shm-dmitry/auto_close_window/3d/mechanics-v2-window-clampwindow-clamp-4.stl

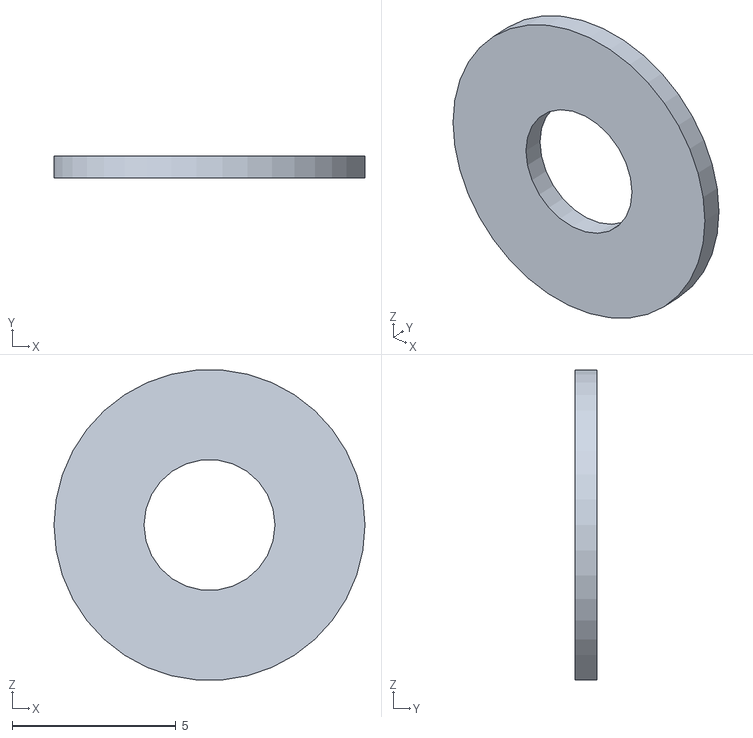
[picture p15: CAD file, 2024-10-09]
3d/mechanics-v2-window-clampwindow-clamp-4.stl
9.50 x 0.68 x 9.47
