shm-dmitry/auto_close_window/3d/mechanics-v2-pdu2pdu-box-up.stl

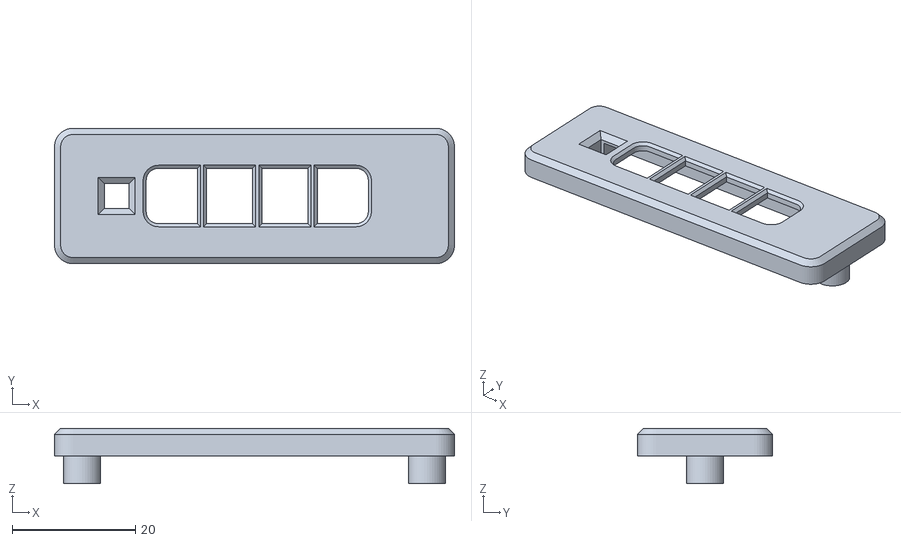
[picture p16: CAD file, 2024-10-09]
3d/mechanics-v2-pdu2pdu-box-up.stl
65.0 x 22.0 x 9.00
