shm-dmitry/auto_close_window/3d/mechanics-v2-mmmm-charge-button.stl

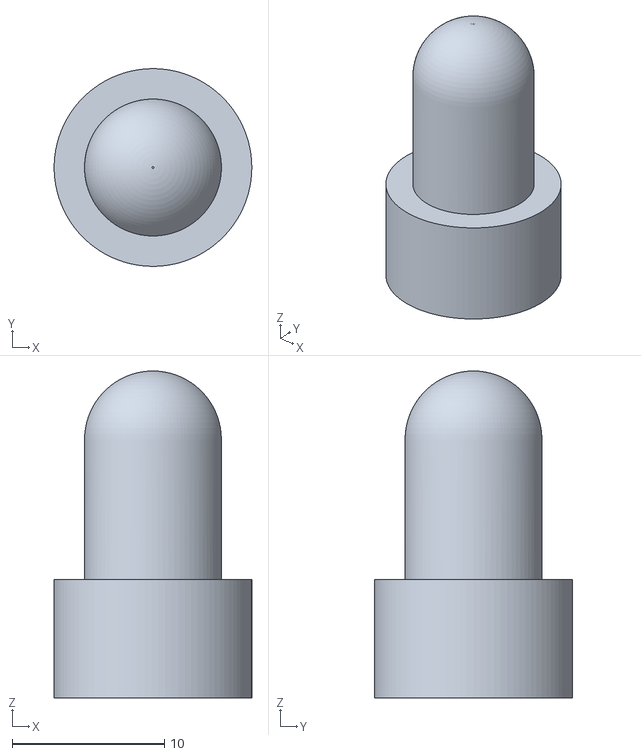
[picture p17: CAD file, 2024-10-09]
3d/mechanics-v2-mmmm-charge-button.stl
13.0 x 13.0 x 21.5
