shm-dmitry/auto_close_window/3d/mechanics-v2-servo_platesw420-adapter.stl

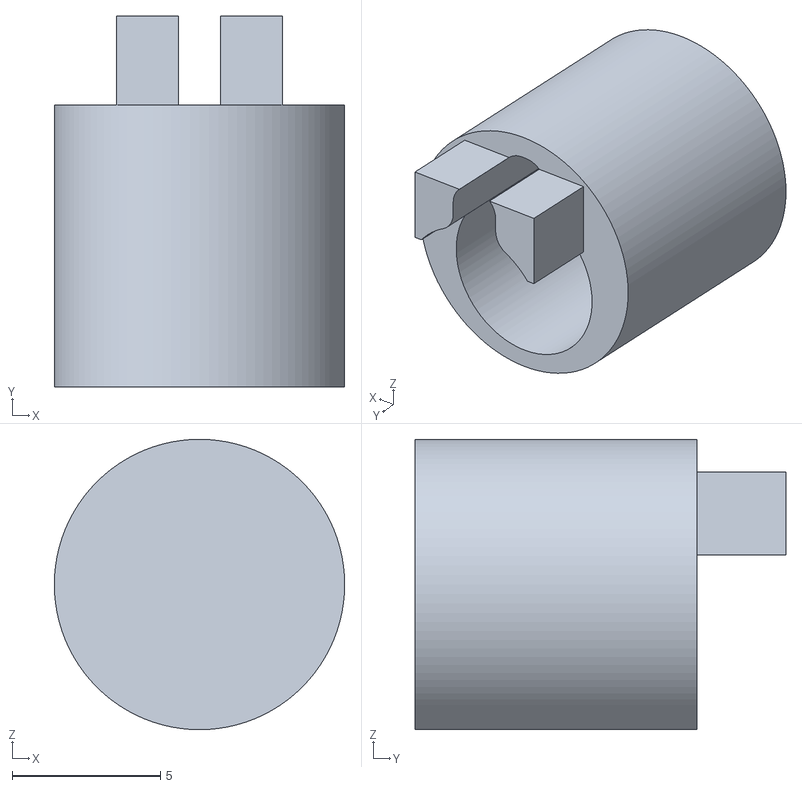
[picture p18: CAD file, 2024-10-09]
3d/mechanics-v2-servo_platesw420-adapter.stl
9.80 x 12.5 x 9.80
