shm-dmitry/auto_close_window/3d/mechanics-v2-hmhm-down.stl

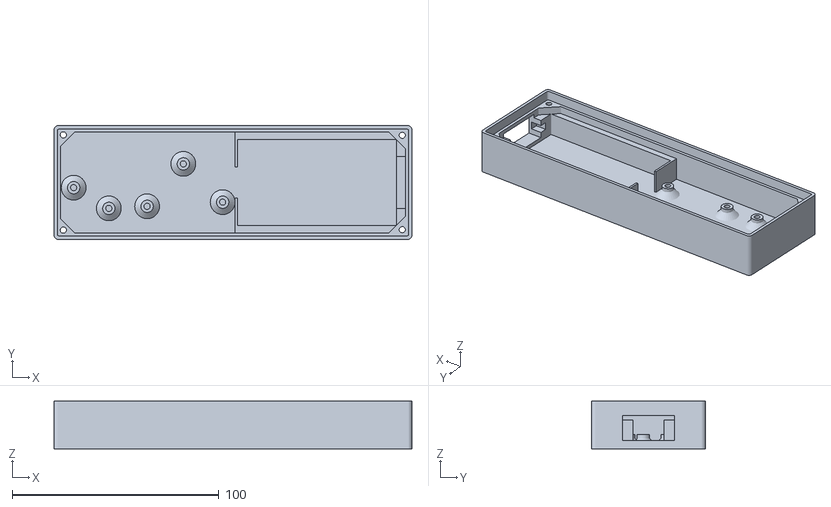
[picture p19: CAD file, 2024-10-09]
3d/mechanics-v2-hmhm-down.stl
173.0 x 55.0 x 23.0
