shm-dmitry/auto_close_window/3d/mechanics-v2-servo_platedebug-wall-support.stl

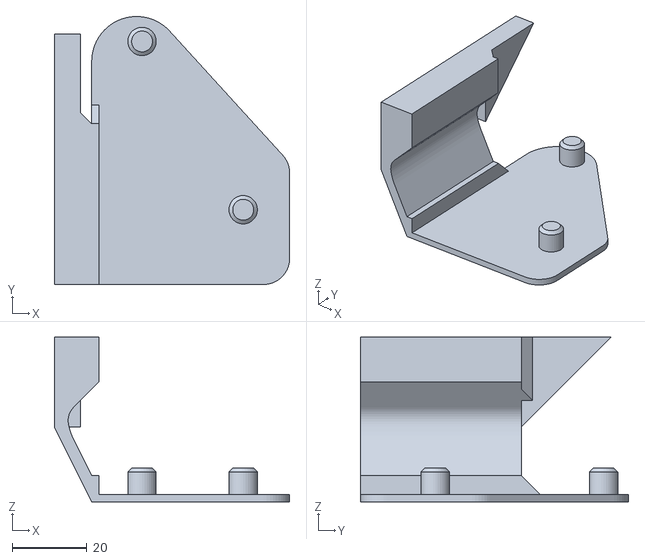
[picture p20: CAD file, 2024-10-09]
3d/mechanics-v2-servo_platedebug-wall-support.stl
63.0 x 71.7 x 44.0
