shm-dmitry/auto_close_window/3d/mechanics-v2-mmmm-charger-port.stl

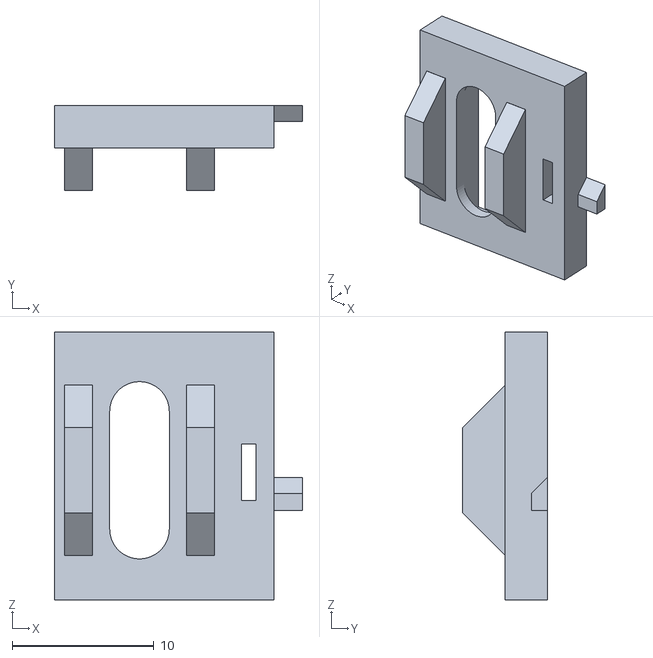
[picture p21: CAD file, 2024-10-09]
3d/mechanics-v2-mmmm-charger-port.stl
17.5 x 6.00 x 18.9
