shm-dmitry/auto_close_window/3d/mechanics-v2-mmmm-charger-cup.stl

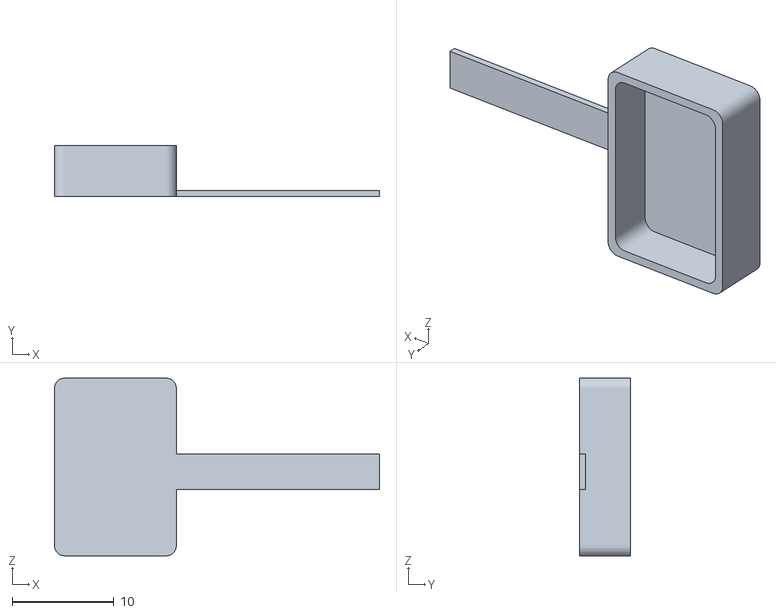
[picture p22: CAD file, 2024-10-09]
3d/mechanics-v2-mmmm-charger-cup.stl
32.0 x 5.00 x 17.5
