shm-dmitry/auto_close_window/3d/mechanics-v2-hmhm-glass.stl

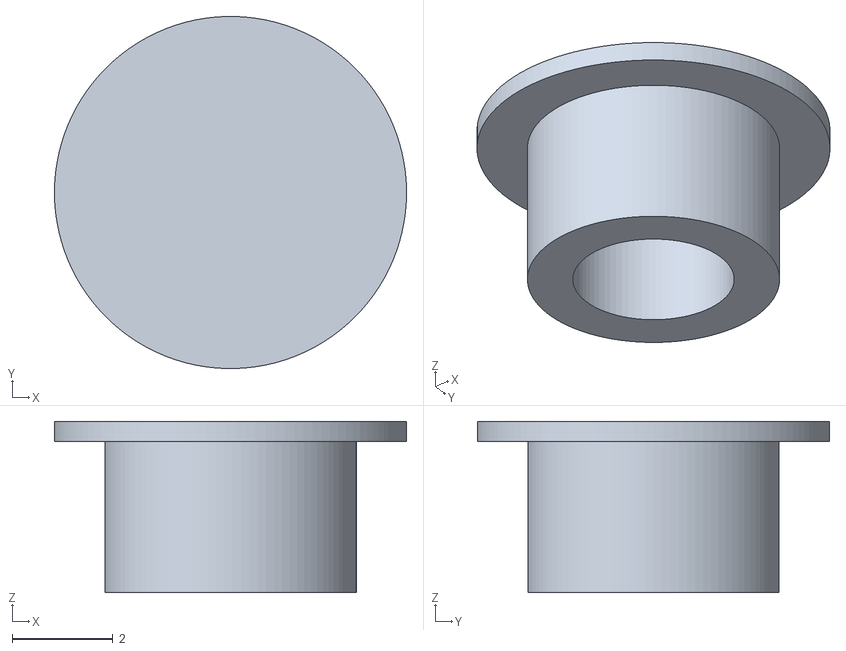
[picture p23: CAD file, 2024-10-09]
3d/mechanics-v2-hmhm-glass.stl
7.00 x 7.00 x 3.40
