shm-dmitry/auto_close_window/3d/mechanics-v2-servolimiters.stl

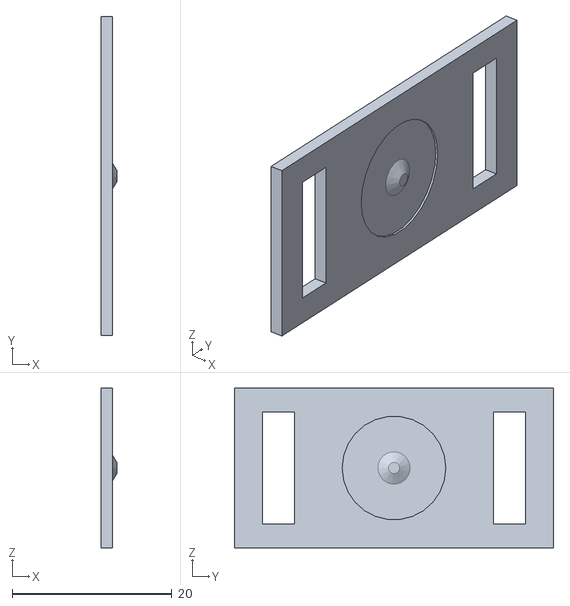
[picture p24: CAD file, 2024-10-09]
3d/mechanics-v2-servolimiters.stl
2.00 x 40.0 x 20.0
