shm-dmitry/auto_close_window/3d/mechanics-v2-servoservo-hand.stl

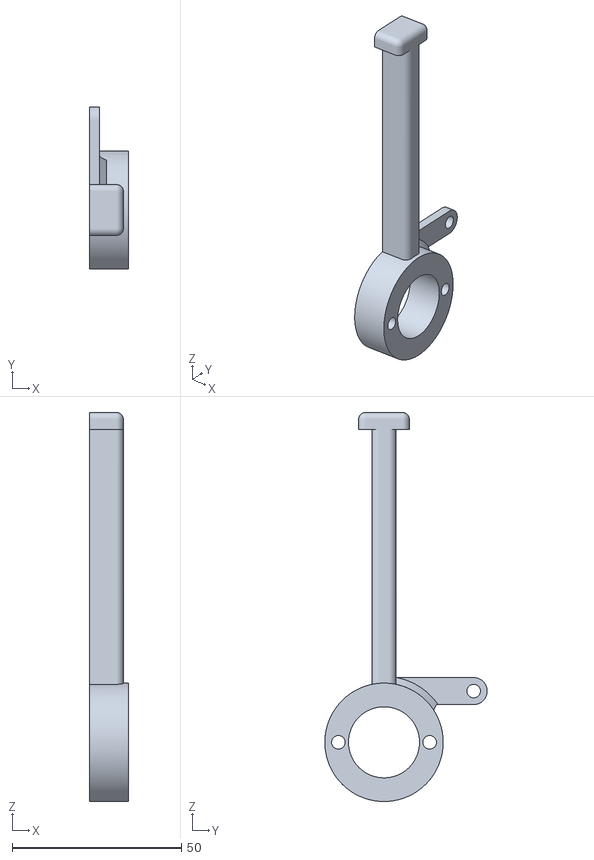
[picture p25: CAD file, 2024-10-09]
3d/mechanics-v2-servoservo-hand.stl
11.5 x 48.0 x 115.0
