shm-dmitry/auto_close_window/3d/mechanics-v2-servo_plateservo-holder-cabel.stl

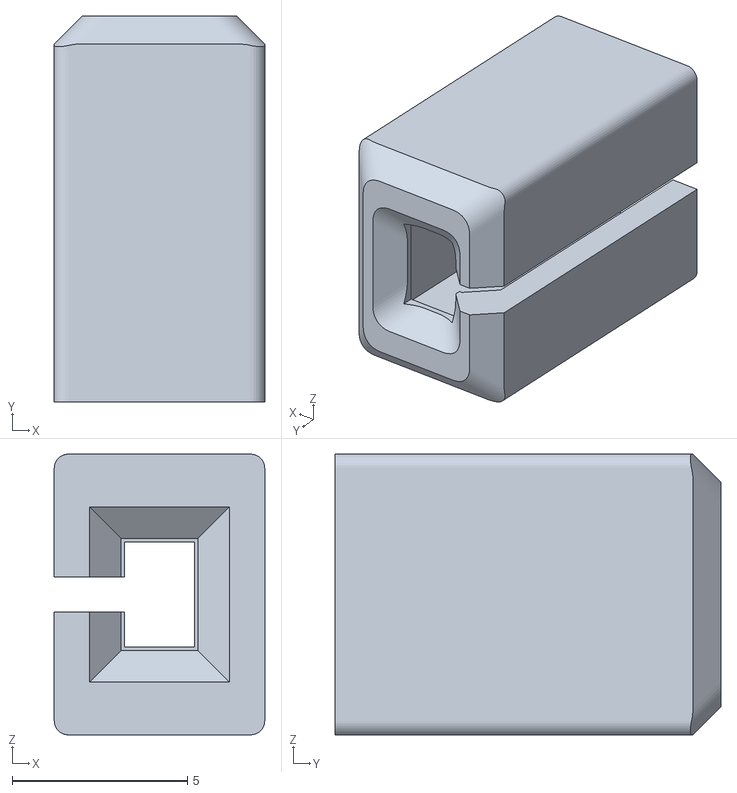
[picture p26: CAD file, 2024-10-09]
3d/mechanics-v2-servo_plateservo-holder-cabel.stl
6.00 x 11.0 x 8.00
