shm-dmitry/auto_close_window/3d/mechanics-v2-servolimit-switch-extboard-holder.stl

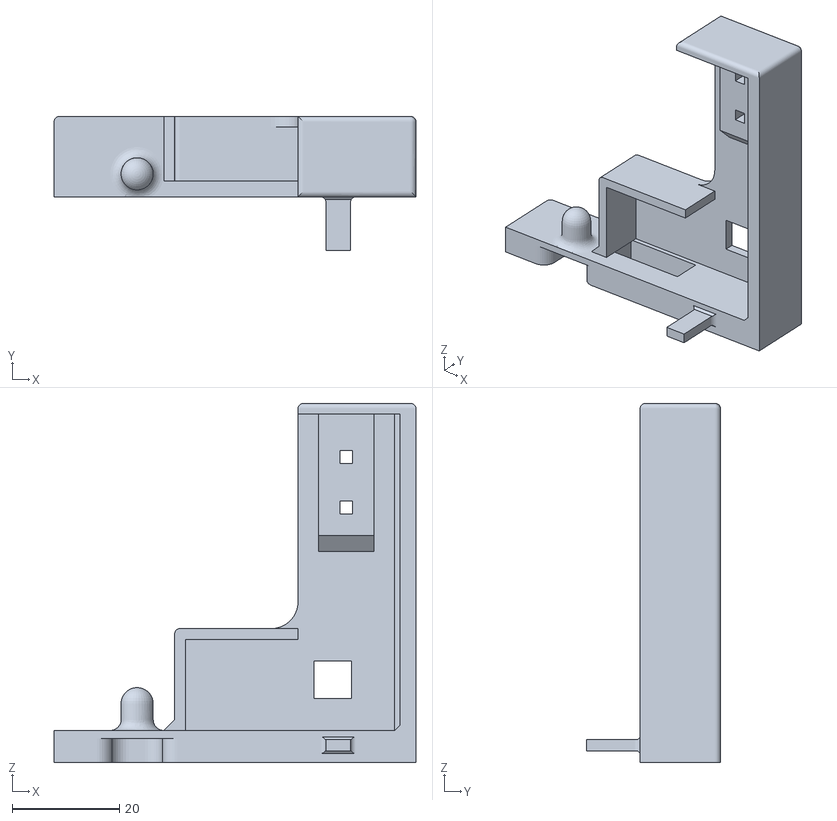
[picture p27: CAD file, 2024-10-09]
3d/mechanics-v2-servolimit-switch-extboard-holder.stl
67.5 x 25.0 x 67.0
