shm-dmitry/auto_close_window/3d/mechanics-v2-servolimit-switch-cabel-holder.stl

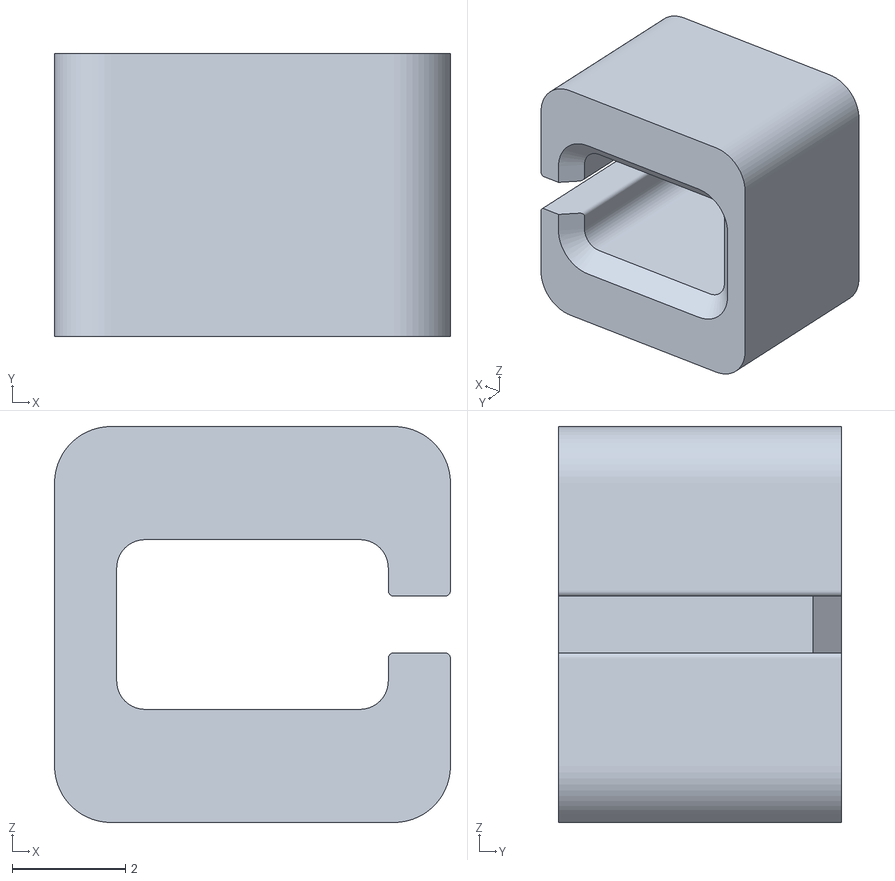
[picture p28: CAD file, 2024-10-09]
3d/mechanics-v2-servolimit-switch-cabel-holder.stl
7.00 x 5.00 x 7.00
