shm-dmitry/auto_close_window/3d/mechanics-v2-servo_platemicrophone-air-ring.stl

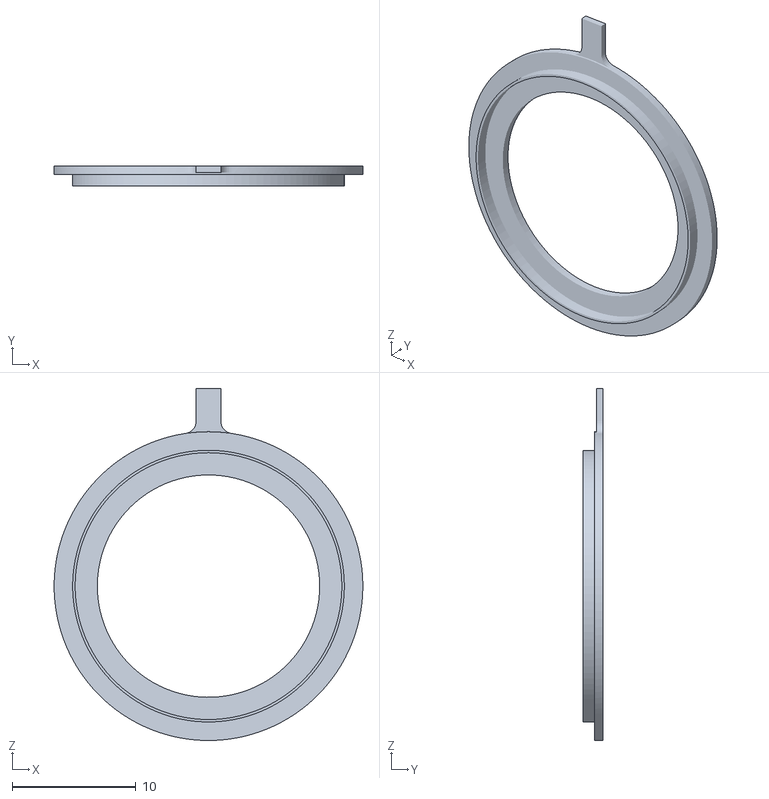
[picture p29: CAD file, 2024-10-09]
3d/mechanics-v2-servo_platemicrophone-air-ring.stl
25.0 x 1.64 x 28.5
