shm-dmitry/auto_close_window/3d/mechanics-v2-hmhm-button.stl

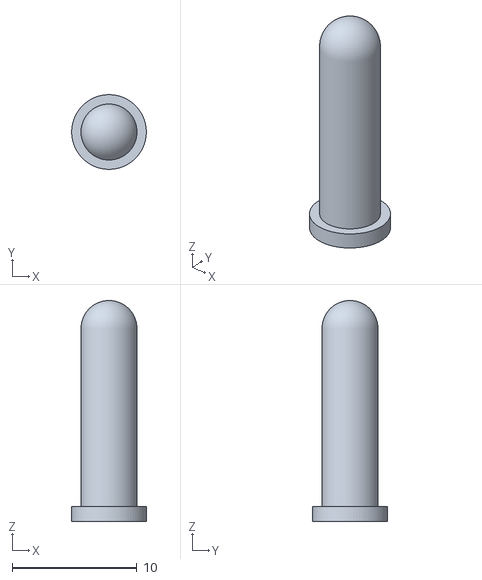
[picture p30: CAD file, 2024-10-09]
3d/mechanics-v2-hmhm-button.stl
6.00 x 6.00 x 17.8
