shm-dmitry/auto_close_window/3d/mechanics-v2-window-clamplimit-switch-cup-small.stl

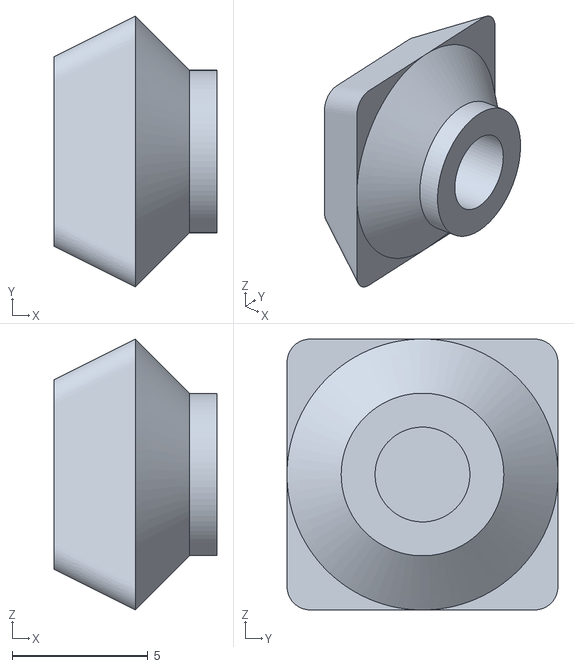
[picture p31: CAD file, 2024-10-09]
3d/mechanics-v2-window-clamplimit-switch-cup-small.stl
6.00 x 10.0 x 10.0
