shm-dmitry/auto_close_window/3d/mechanics-v2-window-clampwindow-clamp-1.stl

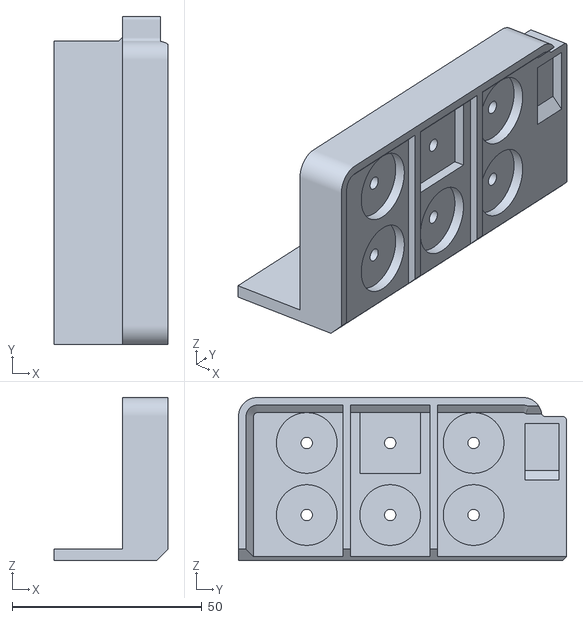
[picture p32: CAD file, 2024-10-09]
3d/mechanics-v2-window-clampwindow-clamp-1.stl
30.0 x 86.5 x 43.0
