shm-dmitry/auto_close_window/3d/mechanics-v2-rubberrubber-tensioner.stl

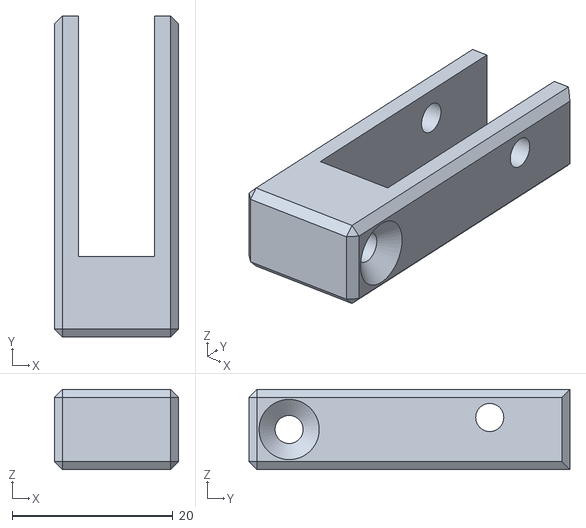
[picture p33: CAD file, 2024-10-09]
3d/mechanics-v2-rubberrubber-tensioner.stl
15.5 x 40.0 x 10.0
