shm-dmitry/auto_close_window/3d/mechanics-v2-window-clamplimit-switch-cup.stl

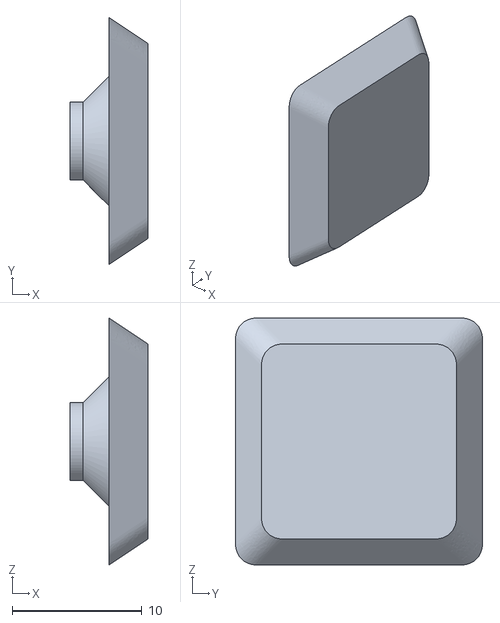
[picture p34: CAD file, 2024-10-09]
3d/mechanics-v2-window-clamplimit-switch-cup.stl
6.00 x 19.0 x 19.0
