shm-dmitry/auto_close_window/3d/mechanics-v2-hmhm-charger-port-cup.stl

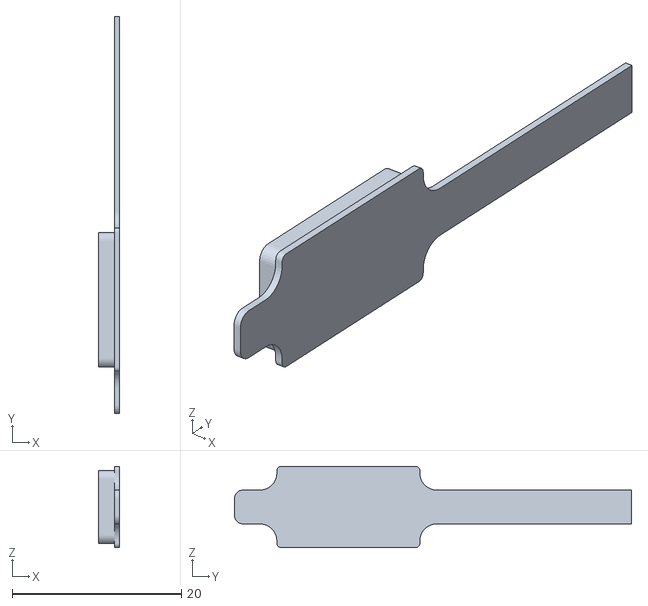
[picture p35: CAD file, 2024-10-09]
3d/mechanics-v2-hmhm-charger-port-cup.stl
2.50 x 46.9 x 9.60
