shm-dmitry/auto_close_window/3d/mechanics-v2-window-clampwindow-clamp-2.stl

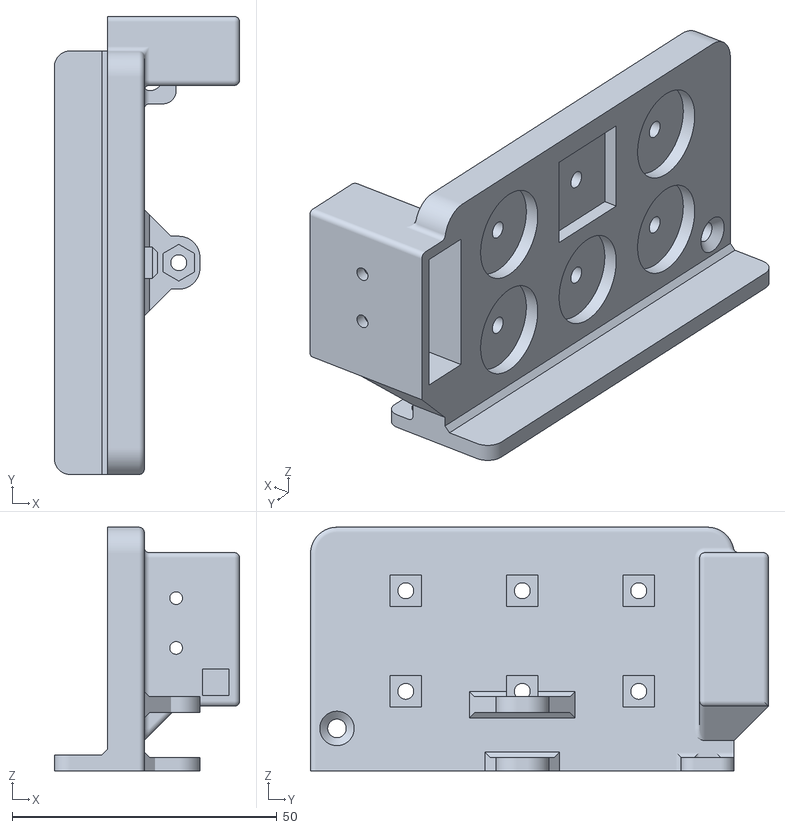
[picture p36: CAD file, 2024-10-09]
3d/mechanics-v2-window-clampwindow-clamp-2.stl
35.0 x 86.5 x 46.0
