shm-dmitry/auto_close_window/3d/mechanics-v2-hmhm-up.stl

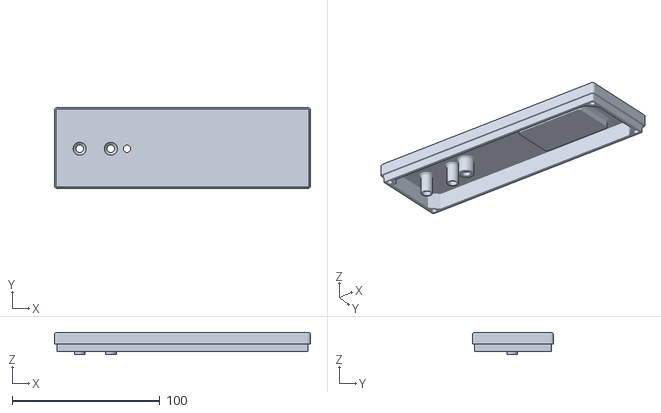
[picture p37: CAD file, 2024-10-09]
3d/mechanics-v2-hmhm-up.stl
173.0 x 55.0 x 15.0
