shm-dmitry/auto_close_window/3d/mechanics-v2-mmmm-box-up.stl

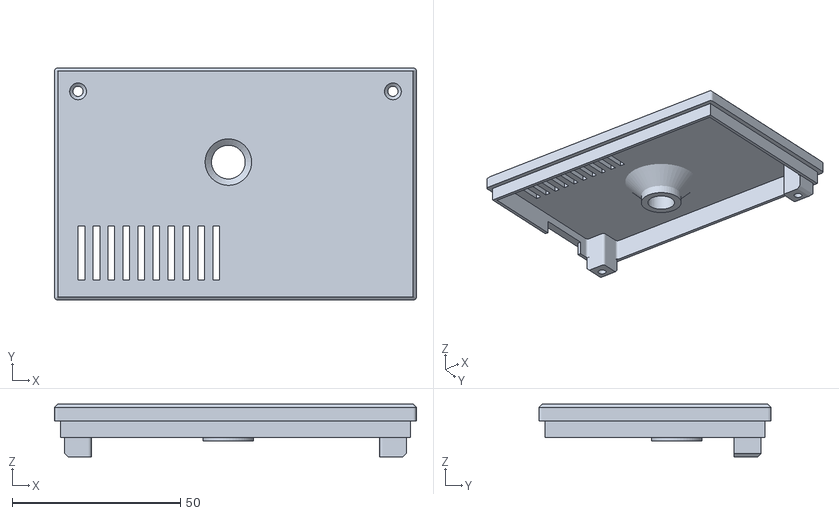
[picture p38: CAD file, 2024-10-09]
3d/mechanics-v2-mmmm-box-up.stl
107.5 x 69.0 x 15.7
