shm-dmitry/auto_close_window/3d/mechanics-v2-servo_plateservo-holder-v2.stl

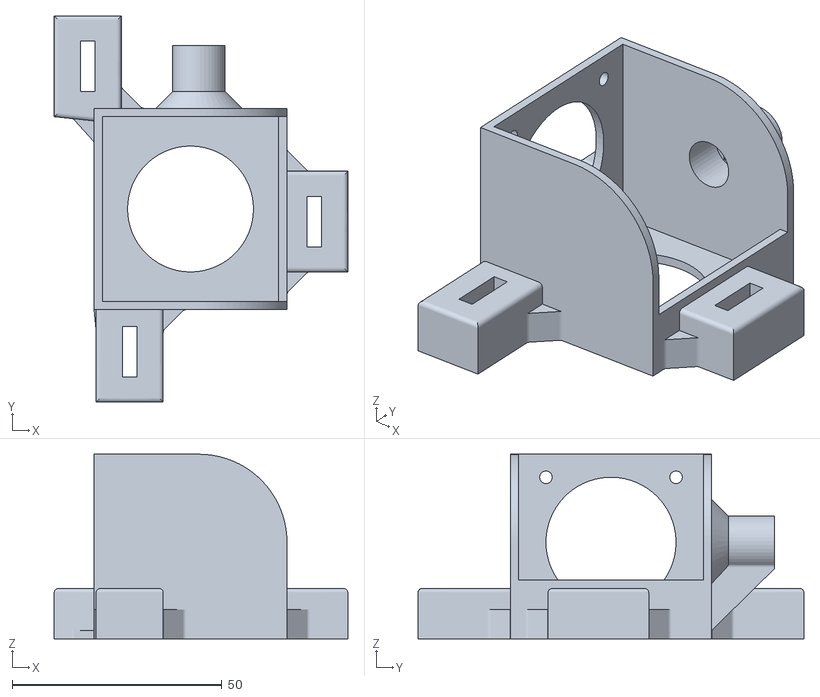
[picture p39: CAD file, 2024-09-12]
3d/mechanics-v2-servo_plateservo-holder-v2.stl
70.0 x 92.0 x 44.0
