shm-dmitry/auto_close_window/src/main_module/main/stepper/stepper_init.c

#include "stepper_init.h"

#include "stepper_adc.h"

#include "stepper_executor.h"
#include "../controller/controller_mqtt.h"

#include "esp_attr.h"
#include "../log/log.h"
#include "sdkconfig.h"

#include "freertos/FreeRTOS.h"

#include "string.h"

#define STEPPER_COMMAND_TASK_STACK_SIZE 4096

#define STEPPER_ENABLE_NOISE_ALARM  		true
#define STEPPER_ENABLE_NOISE_AUTO_DEALARM	true

#define STEPPER_NOISE_ALARM_DEGLICH   		2
#define STEPPER_NOISE_AUTO_DEALARM_DEGLICH	(10*1000/10)

static volatile bool stepper_noise_alarm_enabled = true;

#if STEPPER_ENABLE_NOISE_ALARM
static void stepper_noise_alarm_task(void*);
#endif

void stepper_init() {
	_ESP_LOGI(LOG_STEPPER, "Initializing ADC channels...");

	t_endstops * endstops = stepper_adc_init();

	_ESP_LOGI(LOG_STEPPER, "Initializing stepper executor controller");

    stepper_executor_init(endstops);

#if STEPPER_ENABLE_NOISE_ALARM
	_ESP_LOGI(LOG_STEPPER, "Starting check noise alarm thread");

	xTaskCreate(stepper_noise_alarm_task, "noise alarm task", STEPPER_COMMAND_TASK_STACK_SIZE, NULL, 10, NULL);
#endif

	_ESP_LOGI(LOG_STEPPER, "Stepper initialied");
}

#if STEPPER_ENABLE_NOISE_ALARM
static void stepper_noise_alarm_task(void*) {
	uint8_t deglichON = 0;
#if STEPPER_ENABLE_NOISE_AUTO_DEALARM
	uint16_t deglichOFF = 0;
#endif

	while(true) {
		if (stepper_adc_is_noise_alarm_fired()) {
			if (deglichON >= STEPPER_NOISE_ALARM_DEGLICH) {
				if (stepper_noise_alarm_enabled) {
					stepper_executor_on_alarm();
				}
			} else {
				deglichON++;
			}
		} else {
			deglichON = 0;
#if STEPPER_ENABLE_NOISE_AUTO_DEALARM
			if (stepper_executor_is_in_error()) {
				if (deglichOFF >= STEPPER_NOISE_AUTO_DEALARM_DEGLICH) {
					stepper_executor_cancel_error();
				} else {
					deglichOFF++;
				}
			} else {
				deglichOFF = 0;
			}
#endif
		}

		if (!stepper_noise_alarm_enabled && stepper_executor_is_in_error()) {
			stepper_executor_cancel_error();
			deglichON = 0;
#if STEPPER_ENABLE_NOISE_AUTO_DEALARM
			deglichOFF = 0;
#endif
		}

		do {
			vTaskDelay(10 / portTICK_PERIOD_MS);
		} while (!stepper_noise_alarm_enabled && !stepper_executor_is_in_error());
	}
}
#endif

void stepper_calibrate() {
	stepper_adc_lsw_enable(true);
	stepper_executor_calibrate();
}

void stepper_cancel_error() {
	stepper_executor_cancel_error();
}

bool stepper_is_now_executing_move_to(uint8_t percent) {
	if (percent > 100) {
		return false;
	}

	return stepper_executor_is_now_executing_move_to(percent);
}

void stepper_move_to(uint8_t percent) {
	if (percent > 100) {
		percent = 100;
	}

	stepper_executor_moveto(percent);
}

void stepper_cancel() {
	stepper_executor_cancel();
}

void stepper_noise_alarm_enable(bool enable) {
	if (stepper_noise_alarm_enabled != enable) {
		_ESP_LOGI(LOG_STEPPER, "Noise alarm : %s", (enable ? "ENABLED" : "DISABLED"));
	}

	stepper_noise_alarm_enabled = enable;
	controller_mqtt_noise_alarm_enabled(enable);
}

void stepper_limit_switch_enable(bool enable) {
	stepper_adc_lsw_enable(enable);
}

void stepper_allow_unlock_on_endpos(bool value) {
	stepper_executor_allow_unlock_on_endpos(value);
}

void stepper_publish_status() {
	stepper_noise_alarm_enable(stepper_noise_alarm_enabled);
	stepper_adc_publish_status();
	stepper_executor_publish_status();
}
