shm-dmitry/auto_close_window/src/main_module/main/stepper/stepper_executor.h

#ifndef MAIN_STEPPER_STEPPER_EXECUTOR_H_
#define MAIN_STEPPER_STEPPER_EXECUTOR_H_

#include "stepper_def.h"

#include "stdint.h"
#include "stdbool.h"

void stepper_executor_init(t_endstops * endstops);

void stepper_executor_calibrate();
void stepper_executor_moveto(uint8_t percent);
bool stepper_executor_is_now_executing_move_to(uint8_t percent);
void stepper_executor_cancel();
void stepper_executor_on_alarm();
void stepper_executor_cancel_error();
bool stepper_executor_is_in_error();
void stepper_executor_publish_status();
void stepper_executor_allow_unlock_on_endpos(bool value);
void stepper_executor_publish_status();

#endif /* MAIN_STEPPER_STEPPER_EXECUTOR_H_ */
