shm-dmitry/auto_close_window/src/main_module/main/stepper/stepper_one_step.h

#ifndef MAIN_STEPPER_STEPPER_ONE_STEP_H_
#define MAIN_STEPPER_STEPPER_ONE_STEP_H_

void stepper_one_step_init();
void stepper_do_one_step();

void stepper_set_open();
void stepper_set_close();

#endif /* MAIN_STEPPER_STEPPER_ONE_STEP_H_ */
